ayulikhar/Aurum_MakerMania_2026/images/WhatsApp Image 2026-06-24 at 1.21.38 PM (1).jpeg

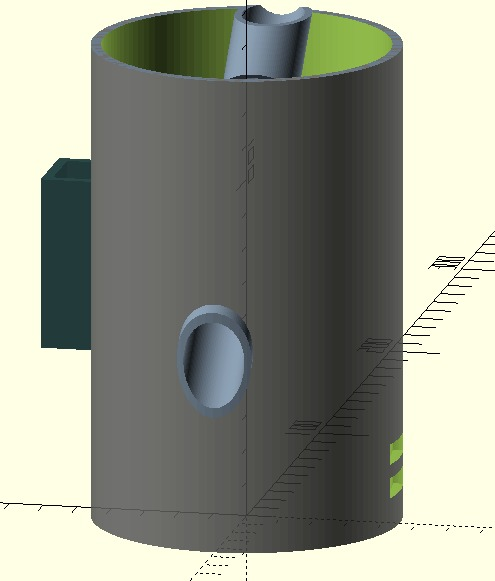
images/WhatsApp Image 2026-06-24 at 1.21.38 PM (1).jpeg
